bocoroth/mdlware/MDLSynth/MDL-01 VCO/sim/MDL-01 VCO.asc

C2: cap; 100pF
C3: cap; 2.2nF
C4: cap; 10µ; V=25 Irms=8.06 Rser=0.00577565 Lser=0 mfg="KEMET" pn="C1210C106K3PAC" type="X5R"
C6: cap; 1µF; V=50 Irms=0 Rser=0.008 Lser=0
C7: cap; 100nF
C8: cap; 100nF
C9: cap; 1nF; V=50 Irms=0 Rser=0.008 Lser=0
C10: cap; 1µF; V=50 Irms=0 Rser=0.008 Lser=0
C11: cap; 1µF; V=50 Irms=0 Rser=0.008 Lser=0 mfg="TDK" pn="C3225X7RlHlO5M" type="X7R"
D1: diode; 1N4148
D2: diode; 1N4148
D3: diode; 1N4148
D4: diode; 1N4148
D5: diode; 1N4148
J1: njf; 2N5457
NTC1: res; 10K
Q1: npn; 2N3904
Q2: npn; 2N3904
R1: res; 100K
R2: res; 100K
R3: res; 1811
R4: res; 30K
R5: res; 20K
R6: res; 189
R7: res; 1.5Meg
R8: res; 100K
R9: res; 1K
R10: res; 100K
R11: res; 2K
R12: res; 220K
R13: res; 47K
R14: res; 10K
R15: res; 10K
R16: res; 47K
R17: res; 56K
R21: res; 100K
R22: res; 200K
R23: res; 22K
R24: res; 47K
R25: res; 100K
R26: res; 10K
R27: res; 5.1K
R28: res; 50K
R29: res; 50K
R30: res; 10K
R31: res; 10K
R32: res; 20K
R33: res; 1Meg
R34: res; 1K
R35: res; 1Meg
R36: res; 1K
R37: res; 1.8K
R38: res; 8.2K
R39: res; 1K
R40: res; 200K
R41: res; 10K
R42: res; 1K
R43: res; 1K
R44: res; 1K
R45: res; 1K
R46: res; 1Meg
R47: res; 10K
R48: res; 3.3K
R49: res; 3.9K
R50: res; 1K
R51: res; 3.3K
R52: res; 6.8K
R53: res; 2K
R54: res; 1002.5
R55: res; 100K
R56: res; 47K
R57: res; 3.9K
U1: opamp2; TL074
U1a: opamp2; TL074
U1b: opamp2; TL074
U1c: opamp2; TL074
U1d: opamp2; TL074
U2: opamp2; TL074
U2a: opamp2; TL074
U2b: opamp2; TL074
U3: opamp2; TL074
U3b: opamp2; TL074
U4: opamp2; TL074
U5: opamp2; TL074
U6: opamp2; TL074
U7: opamp2; TL074
V1: voltage; 12V
V2: voltage; 12V
V3: voltage; 2V
V4: voltage; PWL(0 0 1000ms 0 2000ms 10V)
V5: voltage; PWL(0 -12V 70ms -2V 119ms -2V 120ms -12V 149ms -12V 150ms -1V 199ms -1V 200ms -12V)
Named nets: 0, Vcc, Vee, CV1, SAW, CV2, CV3, PULSE, RAMP, SQUARE, TRIANGLE, SINE
.tran 0 1200ms 1000ms
Base Freq
TRIM
25-TURN
B2K
HI-FREQ
TRIM
MANUAL
FREQ
B100K
MANUAL
FREQ
SWITCH
.MODEL 2N5457 NJF(Beta=1.125m Betatce=-500m Rd=1 Rs=1 Lambda=2.3m Vto=-1.372 Vtotc=-2.5m Is=181.3f Isr=1.747p N=1 Nr=2 Xti=3 Alpha=2.543u Vk=152.2 Cgd=4p M=311.4m Pb=500m Fc=500m Cgs=4.627p Kf=1.045e-002f Af=1)
* TL072 OPERATIONAL AMPLIFIER "MACROMODEL" SUBCIRCUIT
* CREATED USING PARTS RELEASE 4.01 ON 06/16/89 AT 13:08
* (REV N/A)      SUPPLY VOLTAGE: +/-15V
* CONNECTIONS:   NON-INVERTING INPUT
*                | INVERTING INPUT
*                | | POSITIVE POWER SUPPLY
*                | | | NEGATIVE POWER SUPPLY
*                | | | | OUTPUT
*                | | | | |
.SUBCKT TL074    1 2 3 4 5
*
  C1   11 12 3.498E-12
  C2    6  7 15.00E-12
  DC    5 53 DX
  DE   54  5 DX
  DLP  90 91 DX
  DLN  92 90 DX
  DP    4  3 DX
  EGND 99  0 POLY(2) (3,0) (4,0) 0 .5 .5
  FB    7 99 POLY(5) VB VC VE VLP VLN 0 4.715E6 -5E6 5E6 5E6 -5E6
  GA    6  0 11 12 282.8E-6
  GCM   0  6 10 99 8.942E-9
  ISS   3 10 DC 195.0E-6
  HLIM 90  0 VLIM 1K
  J1   11  2 10 JX
  J2   12  1 10 JX
  R2    6  9 100.0E3
  RD1   4 11 3.536E3
  RD2   4 12 3.536E3
  RO1   8  5 150
  RO2   7 99 150
  RP    3  4 2.143E3
  RSS  10 99 1.026E6
  VB    9  0 DC 0
  VC    3 53 DC 2.200
  VE   54  4 DC 2.200
  VLIM  7  8 DC 0
  VLP  91  0 DC 25
  VLN   0 92 DC 25
.MODEL DX D(IS=800.0E-18)
.MODEL JX PJF(IS=15.00E-12 BETA=270.1E-6 VTO=-1)
.ENDS
Power Supply
CV Summing
Exponential Converter
Saw Core
Pulse
Attenuator
Ramp Converter
Square Converter
Triangle Converter
Sine Converter
Tests
1V/Oct
TRIM
25-TURN
B2K
Well-matched
